namor5772/Alti_ESP32S3/Extra/Alti_ESP32S3_bak.ino

/*
  Blink

  Turns an LED on for one second, then off for one second, repeatedly.

  Most Arduinos have an on-board LED you can control. On the UNO, MEGA and ZERO
  it is attached to digital pin 13, on MKR1000 on pin 6. LED_BUILTIN is set to
  the correct LED pin independent of which board is used.
  If you want to know what pin the on-board LED is connected to on your Arduino
  model, check the Technical Specs of your board at:
  https://www.arduino.cc/en/Main/Products

  modified 8 May 2014
  by Scott Fitzgerald
  modified 2 Sep 2016
  by Arturo Guadalupi
  modified 8 Sep 2016
  by Colby Newman

  This example code is in the public domain.

  https://www.arduino.cc/en/Tutorial/BuiltInExamples/Blink
*/
// global variables
uint32_t chipId = 0;
int i = 0;

// the setup function runs once when you press reset or power the board
void setup() {
  Serial.begin(115200);

  for (i = 0; i < 17; i = i + 8) {
    chipId |= ((ESP.getEfuseMac() >> (40 - i)) & 0xff) << i;
  }
  Serial.printf("ESP32 Chip model = %s Rev %d\n", ESP.getChipModel(), ESP.getChipRevision());
  Serial.printf("This chip has %d cores\n", ESP.getChipCores());
  Serial.print("Chip ID: ");
  Serial.print(chipId);
  Serial.println("\n");

  // initialize digital pin LED_BUILTIN as an output.
  pinMode(LED_BUILTIN, OUTPUT);

  i = 0;
}

// the loop function runs over and over again forever
void loop() {

  digitalWrite(LED_BUILTIN, HIGH);  // turn the LED on (HIGH is the voltage level)
  delay(1000);                      // wait for a second
  digitalWrite(LED_BUILTIN, LOW);   // turn the LED off by making the voltage LOW
  delay(150);                      // wait for a second
  digitalWrite(LED_BUILTIN, HIGH);   // turn the LED off by making the voltage LOW
  delay(150);                      // wait for a second
  digitalWrite(LED_BUILTIN, LOW);   // turn the LED off by making the voltage LOW
  delay(150);                      // wait for a second
  digitalWrite(LED_BUILTIN, HIGH);   // turn the LED off by making the voltage LOW
  delay(150);                      // wait for a second
  digitalWrite(LED_BUILTIN, LOW);   // turn the LED off by making the voltage LOW
  delay(150);                      // wait for a second
  digitalWrite(LED_BUILTIN, HIGH);   // turn the LED off by making the voltage LOW
  delay(150);                      // wait for a second
  digitalWrite(LED_BUILTIN, LOW);   // turn the LED off by making the voltage LOW
  delay(150);                      // wait for a second

    Serial.println(i);
    i++;

}
